DumplingIsNice/2020-energy-monitor-project-team02-mirror/Hardware/LTspice Schematic/Hardware.asc

Cf1: cap; 4.7n
Cf2: cap; 4.7n
Cin1: cap; 470µ; Rser=0.001
Cout1: cap; 47µ; Rser=0.001
D1: diode; 1N4148
Lload1: ind; 40mH
R9: res; {R1}
R10: res; {R1}
R11: res; {R2}
R12: res; {R2}
R13: res; {Rb}
R14: res; {Ra}
R15: res; {R23}
R16: res; {R23}
R17: res; 18k
R18: res; 12K
Ra1: res; 56k
Rb1: res; 3.3k
Reg1: LT1085-5
Rf1: res; 33k
Rf2: res; 33k
Rf4: res; 0.1n
Rin1: res; 33
RL1: res; 100
Rload1: res; {RL}
Rs1: res; 0.56
U3: opamp2; LM324
U4: opamp2; LM324
U5: opamp2; LM324
U6: opamp2; LM324
V1: voltage; 5V
Vsupply1: voltage; SINE(0 {Vp} {F}); AC {Vp} 0
Named nets: 0, 5VDis, Vac, Vis, 5V, Vio, 2V1, Vvo, Vvofilter, Vin, Vvs, Vzero, Viofilter
.ac dec 30 1 1Meg
.lib LM324.lib
Power/Signal Sources
*********************************************************
ELECTENG 209 - Hardware
Models required provided as a starting point.
LM324.lib must be in the same folder.
*********************************************************
AC Source, Load and Sensors
Notes: 
- Ideal 5V source used to generate the frequency plot.
- Switch top rail of op amp to 5VDis for frequency.
- Switch top rail of op amp to 5V for transient (linear regulator).
Notes: 
- Rload is the variable resistor in your load which changes 
  from 5-105 ohms 
- Vsupply is between 12.6-15.4Vrms
- Pmax = 198.2mW
- Imax = 598.7mA
- Vmax = 21.97V
Load
Current Sens 
(Pmax=198.2mW)
(Imax=598.7mA)
Simulation Commands
- Change these as needed
Current Sensor
Notes: 
- Amplifies and level shifts.
Voltage Sensor
Notes: 
- R1a together with Thevenin of Ra & Rb should equal R1b
- Gain = 1, only level shifts.
Power Supply (5V)
Voltage Filter Circuit (1kHz fbreak)
Notes: 
- Change the simulation command to simulate the frequency response.
- The inductor in the load constitute as a low pass filter. 
That filter and the succeeding opAmp contributes to the overall bandwidth.
- The bode plot must be measured with ideal 5V source and relative to
 its input (V(viofilter)/V(vio)).
- Fc = 1/((2*pi)*R*C)
.tran 0 1 0 1m
.ic V(Vin)=8
Notes: 
- 5V DC Linear Regulator, output load will not impact input current.
- Assume: Iin = IL
- Efficency = Power Delivered/Total Power = (IL*VL)/(IL*VDC) 
      // Changing the output load will not impact efficency
.param R1=22k R2=56k
.param Rb=1.5k Ra=4.7k R23=4.7k
Zero-crossing Detector
.param Vp=sqrt(2)*12.6 F=50 RL=16.65
.param Vp=sqrt(2)*15.4 F=50 RL=29
.param Vp=sqrt(2)*15.4 F=50 RL=92.82
7.5VA
7.5VA
2.5VA
Current Filter Circuit (1kHz fbreak)
Notes: 
- Basic comparator with VOH and VOL at Vvo = 2.1V.
- Digital one on first crossing, positively aligned.
Notes: 
- Voltage divider and unity gain voltage
 follower to derive Vshift from power supply.
