DumplingIsNice/2020-energy-monitor-project-team02-mirror/Hardware/LTspice Schematic/Peak Detector.asc

Cpk: cap; 1µ; Rser=0.001
Dpk: diode; 1N4148
R2: res; 10k
R6: res; 10k
R7: res; 10k
R8: res; 10k
Rz: res; 10k
U1: opamp2; LM324
U2: opamp2; LM324
U8: opamp2; LM324
U9: opamp2; LM324
V2: voltage; 0.3V
Named nets: 0, Vvofilter, 5V
Peak Detector Experimental Circuit
